lolothecoder/VeniVidiVici/CAD/Grab_piece2 v7.step

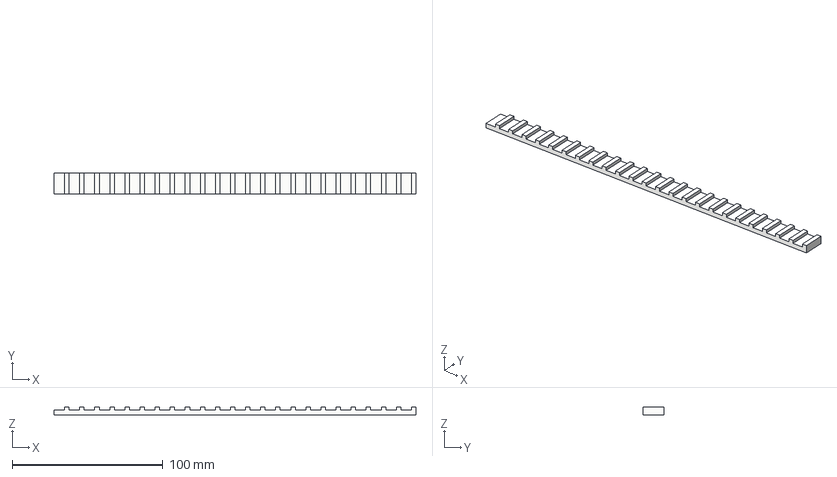
[picture p18: CAD file, 2025-06-16]
CAD/Grab_piece2 v7.step
240.0 x 14.0 x 5.00 mm
