lolothecoder/VeniVidiVici/CAD/Prototype_finale_bearing_support v1.step

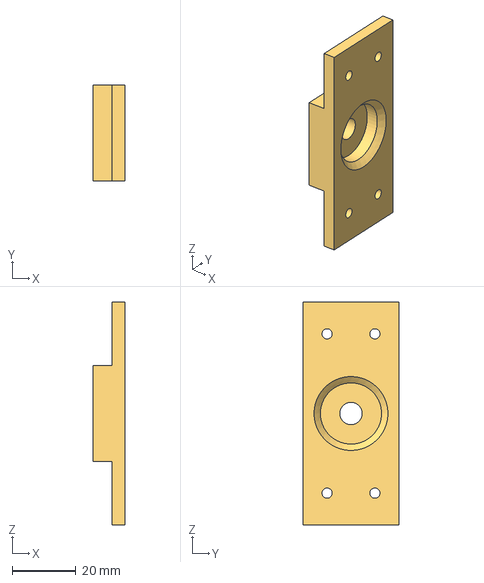
[picture p19: CAD file, 2025-06-16]
CAD/Prototype_finale_bearing_support v1.step
10.0 x 30.0 x 70.0 mm
