lolothecoder/VeniVidiVici/ROSArduinoBridge/sensors_updated.h

#ifdef BATTERY
    #define BATTERY_PIN 15
    #define MIN_ARD_VAL 0
    #define MAX_ARD_VAL 1023
    #define MIN_BAT_VAL 0
    #define MAX_PIN_VAL 5
    #define R7          2200
    #define R8          1100
    void battery_level();
#endif
