lolothecoder/VeniVidiVici/ROSArduinoBridge/custom_servos.ino

#ifdef CUSTOM_SERVOS

void initServos(){
    door.attach(DOOR_PWM);
    ramp.attach(BACKRAMP_PWM);
    door.write(DOOR_CLOSE);
    ramp.write(RAMP_DOWN);
}
void setServo(int i, int pos){
    if (i == DOOR_ID){
        if (pos == DOOR_CLOSE){
            door.write(DOOR_CLOSE);
        } else if (pos == DOOR_OPEN_SHORTCUT){
            door.write(DOOR_OPEN);
        } else {
             Serial.print("Not Valid");
        }
    } else if (i == RAMP_ID){
         if (pos == RAMP_DOWN){
            ramp.write(30);
        } else if (pos == RAMP_UP_SHORTCUT){
            ramp.write(RAMP_UP);
        } else {
             Serial.print("Not Valid");
        }
    } else {
         Serial.print("Not Valid");
    }
}

#endif
