lolothecoder/VeniVidiVici/Tests/measurements.py

#!/usr/bin/env python3
'''Records measurments to a given file. Usage example:

$ ./record_measurments.py out.txt'''
import sys
from rplidar import RPLidar


PORT_NAME = '/dev/ttyUSB0'


def run(path):
    '''Main function'''
    lidar = RPLidar(PORT_NAME)
    outfile = open(path, 'w')
    try:
        print('Recording measurments... Press Crl+C to stop.')
        for quality, angle, distance in lidar.iter_measures():
            line = '\t'.join(str(v) for v in measurment)
            outfile.write(line + '\n')
    except KeyboardInterrupt:
        print('Stoping.')
    lidar.stop()
    lidar.disconnect()
    outfile.close()

if __name__ == '__main__':
    run(sys.argv[1])
